adhamnaeim/pervasive_computing/firmware/LoRaWAN-HelloWorld-radiolib/KiCAD/ESP32-LoRa-SX1262/ESP32-LoRa-SX1262.kicad_sch

## KiCad design firmware/LoRaWAN-HelloWorld-radiolib/KiCAD/ESP32-LoRa-SX1262/ESP32-LoRa-SX1262.kicad_sch (2026-04-27)

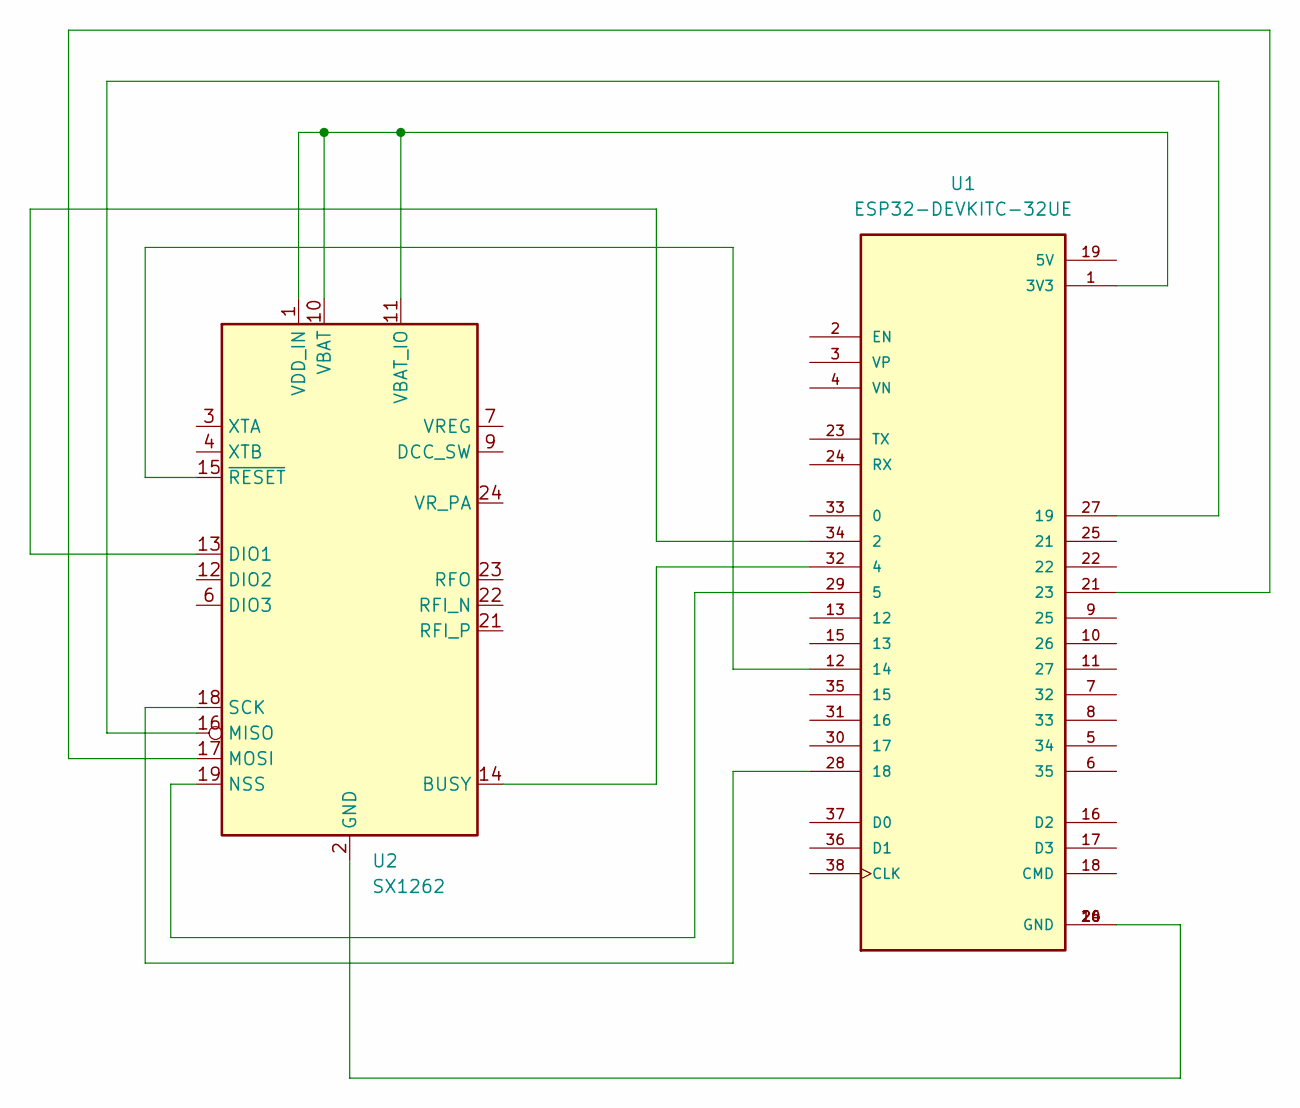
[picture p3: schematic ESP32-LoRa-SX1262.kicad_sch]

Parts:
U1: ESP32-DEVKITC-32UE; ESPRESSIF_ESP32-DEVKITC-32UE; PARTREV V4; DigiKey_Part_Number 1965-ESP32-DEVKITC-32UE-ND
U2: SX1262; QFN-24-1EP_4x4mm_P0.5mm_EP2.6x2.6mm

Connections:
unnamed: U1.1 (3V3), U2.1 (VDD_IN), U2.10 (VBAT), U2.11 (VBAT_IO)
unnamed: U1.12 (14), U2.15 (~RESET)
unnamed: U1.14 (GND), U1.20 (GND), U1.26 (GND), U2.2 (GND), U2.5 (GND), U2.8 (GND), U2.20 (GND), U2.25 (GND)
unnamed: U1.21 (23), U2.17 (MOSI)
unnamed: U1.27 (19), U2.16 (MISO)
unnamed: U1.28 (18), U2.18 (SCK)
unnamed: U1.29 (5), U2.19 (NSS)
unnamed: U1.32 (4), U2.14 (BUSY)
unnamed: U1.34 (2), U2.13 (DIO1)
