adhamnaeim/pervasive_computing/firmware/LoRaWAN-HelloWorld-radiolib/KiCAD/ESP32-LoRa-SX1276/ESP32-LoRa-SX1276.kicad_sch

## KiCad design firmware/LoRaWAN-HelloWorld-radiolib/KiCAD/ESP32-LoRa-SX1276/ESP32-LoRa-SX1276.kicad_sch (2026-04-27)

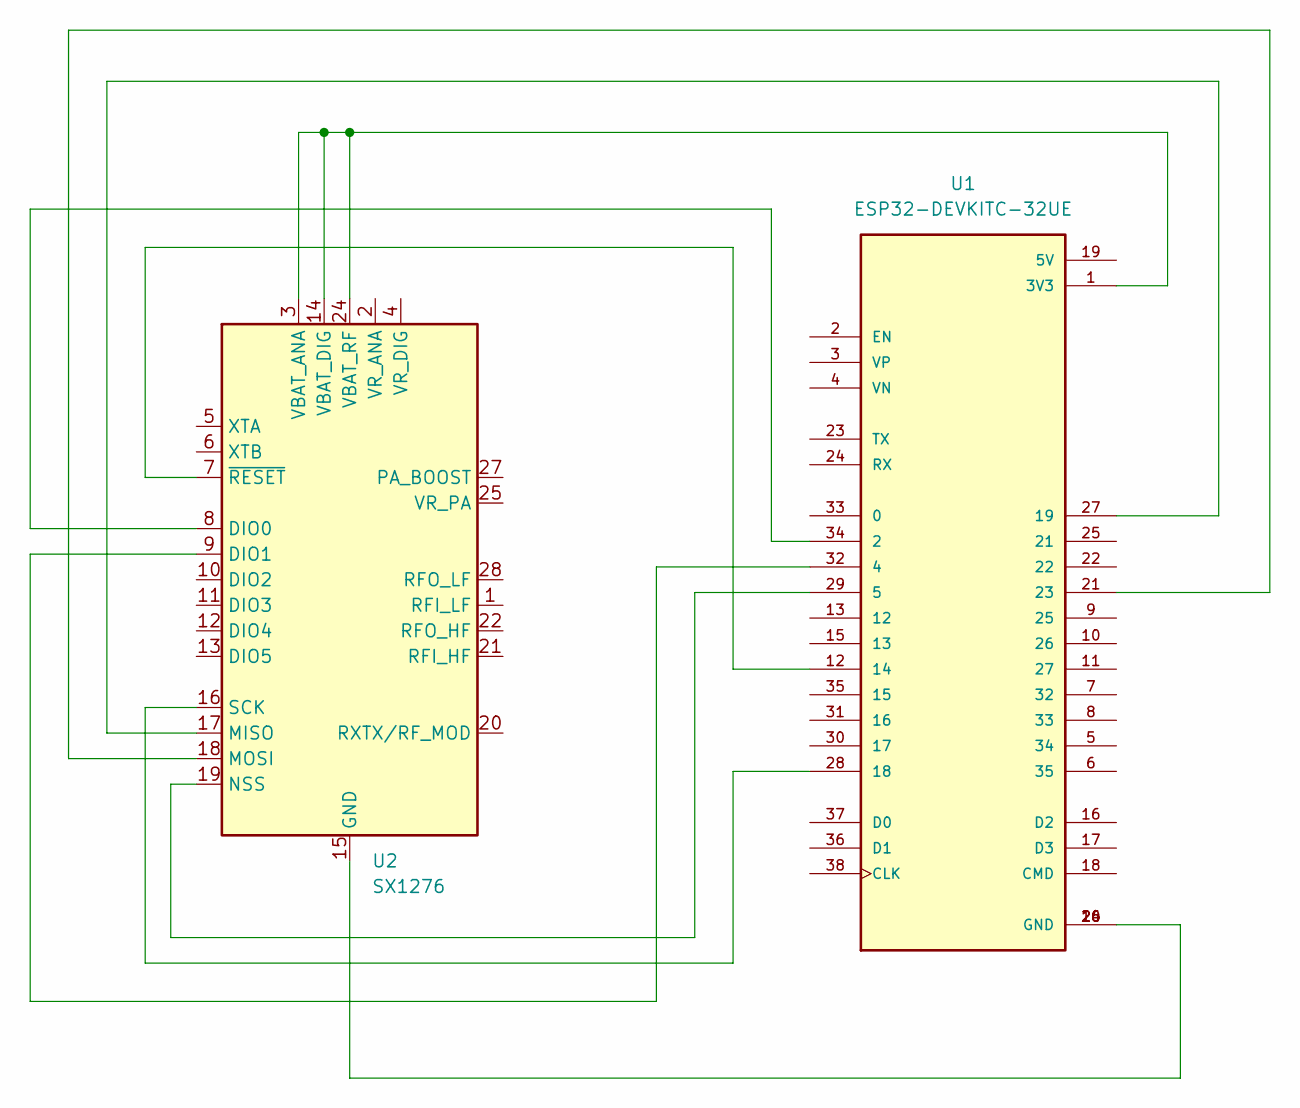
[picture p4: schematic ESP32-LoRa-SX1276.kicad_sch]

Parts:
U1: ESP32-DEVKITC-32UE; ESPRESSIF_ESP32-DEVKITC-32UE; PARTREV V4; DigiKey_Part_Number 1965-ESP32-DEVKITC-32UE-ND
U2: SX1276; QFN-28-1EP_6x6mm_P0.65mm_EP4.8x4.8mm

Connections:
unnamed: U1.1 (3V3), U2.3 (VBAT_ANA), U2.14 (VBAT_DIG), U2.24 (VBAT_RF)
unnamed: U1.12 (14), U2.7 (~RESET)
unnamed: U1.14 (GND), U1.20 (GND), U1.26 (GND), U2.15 (GND), U2.23 (GND), U2.26 (GND), U2.29 (GND)
unnamed: U1.21 (23), U2.18 (MOSI)
unnamed: U1.27 (19), U2.17 (MISO)
unnamed: U1.28 (18), U2.16 (SCK)
unnamed: U1.29 (5), U2.19 (NSS)
unnamed: U1.32 (4), U2.9 (DIO1)
unnamed: U1.34 (2), U2.8 (DIO0)
